Hackuarium/beemos/common/images/beeBackground.jpg

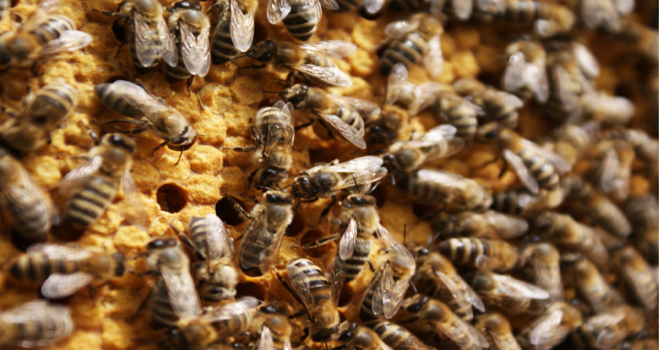
common/images/beeBackground.jpg
