Hackuarium/beemos/common/images/BeeMoSCounterPCB.jpg

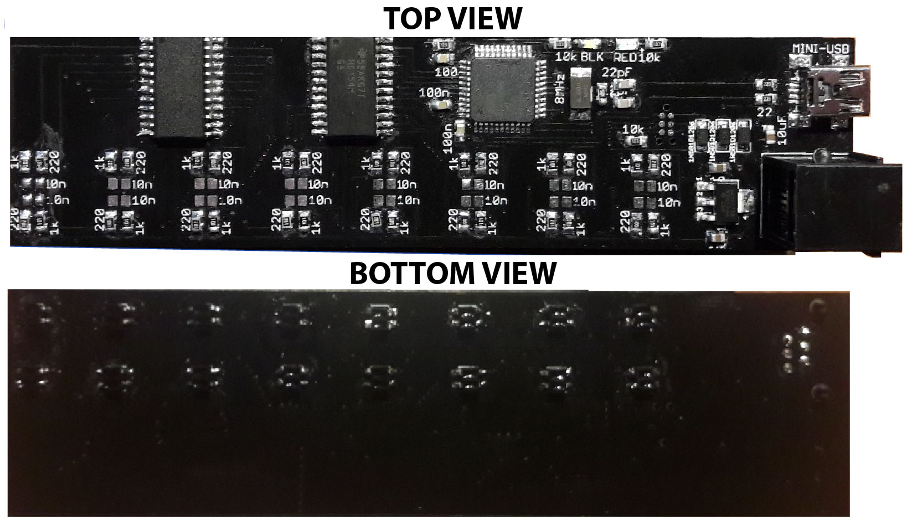
common/images/BeeMoSCounterPCB.jpg
