Hackuarium/beemos/scale-i2c/docs/balance2LoadCellsGlued.jpg

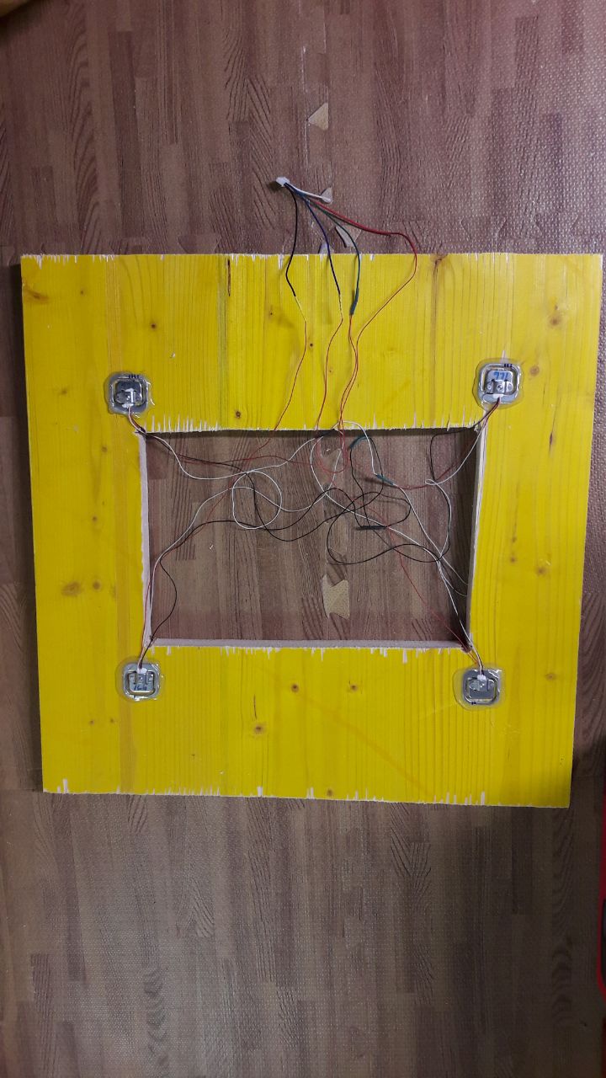
scale-i2c/docs/balance2LoadCellsGlued.jpg
