Hackuarium/beemos/scale-i2c/docs/closeUpBalance2Planed.jpg

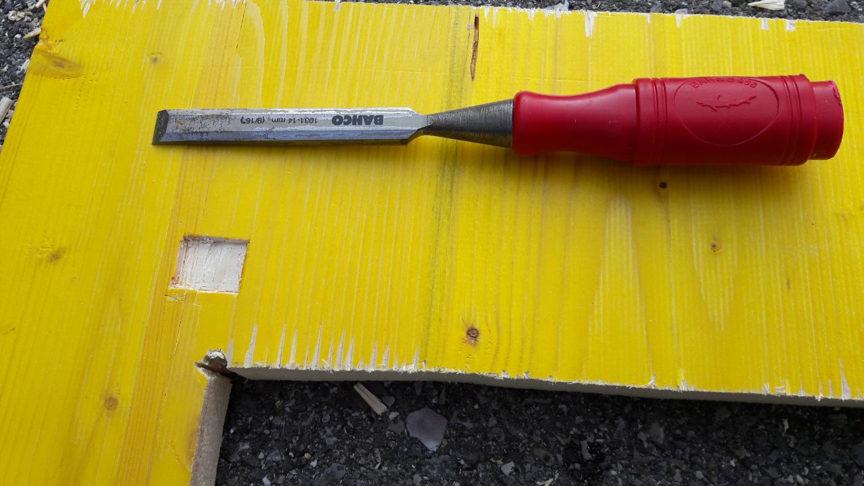
scale-i2c/docs/closeUpBalance2Planed.jpg
