Hackuarium/beemos/counter-i2c/arduino/Counter/Logger.ino

// part of the EEPROM is for the log
// we should be able to save and reload the log

#ifdef LOGGER


#define DATA_SIZE 920
#define DATA_TYPE 0  // LONG

// log is saved in the format ID / in1 / out1 / ... / in8 / out8
// ID is a sequential number
// We expect to add an entry every hour

#define NUMBER_PARAMETERS_TO_LOG  20
#define LOG_ENTRY_LENGTH          NUMBER_PARAMETERS_TO_LOG*2
#define NUMBER_LOGS               DATA_SIZE/LOG_ENTRY_LENGTH

#define FIRST_ADDRESS   1024-LOG_ENTRY_LENGTH*NUMBER_LOGS
#define LAST_ADDRESS   1023

unsigned long lastLog = millis();

void loggerInit() {
  // we need to reload the last ID
  setParameter(PARAM_LOGID, -1);
  for (byte i = 0; i < NUMBER_LOGS; i++) {
    int entryID =  eeprom_read_word((uint16_t*) (getFirstAddress(i)));
    if (entryID > getParameter(PARAM_LOGID)) {
      setParameter(PARAM_LOGID, entryID);
    }
  }
  for (byte i = 1; i < NUMBER_PARAMETERS_TO_LOG; i++) { // on boot counter is equal to 0
    setParameter(i, 0);
  }
  setParameter(PARAM_LOGID, getParameter(PARAM_LOGID) + 1);
  setParameter(PARAM_SECONDS, 0);
}


void writeLog() {
  int firstAddress = getFirstAddress(getParameter(PARAM_LOGID));
  for (byte i = 0; i < NUMBER_PARAMETERS_TO_LOG; i++) {
    eeprom_write_word((uint16_t*)  (firstAddress + i * 2), getParameter(i));
    if (i > 1) setParameter(i, 0);
  }
  setParameter(PARAM_LOGID, getParameter(PARAM_LOGID) + 1);
  lastLog = millis();
}

void readLog(byte entryID) {
  int firstAddress = getFirstAddress(entryID);
  for (byte i = 0; i < NUMBER_PARAMETERS_TO_LOG; i++) {
    setParameter(i, eeprom_read_word((uint16_t*) (firstAddress + i * 2)));
  }
}

int getFirstAddress(int entryID) {
  return FIRST_ADDRESS + LOG_ENTRY_LENGTH * (entryID % NUMBER_LOGS);
}

void formatLog() {
  for (int i = FIRST_ADDRESS; i <= LAST_ADDRESS; i++) {
    eeprom_write_byte(i, 0);
  }
  setParameter(PARAM_LOGID, 0);
}

void printLog(Print* output) {
  for (byte i = 0; i < NUMBER_LOGS; i++) {
    output->print(i);
    output->print(" ");
    int firstAddress = getFirstAddress(i);
    for (byte j = 0; j < NUMBER_PARAMETERS_TO_LOG; j++) {
      output->print((int)eeprom_read_word((uint16_t*) (firstAddress + j * 2)));
      output->print(" ");
    }
    output->println("");
  }
}

NIL_WORKING_AREA(waThreadLogger, 0);
NIL_THREAD(ThreadLogger, arg) {
  loggerInit();
  while (true) {
    nilThdSleepMilliseconds(1000);

    int counter = 0;
    while (counter < getParameter(PARAM_LOGGING_INTERVAL)) {
      nilThdSleepMilliseconds(1000);
      counter++;
    }

    if (getParameter(PARAM_LOGGING_INTERVAL) >= 300) {
      writeLog();
    }
  }
}

void printLoggerHelp(Print * output) {
  output->println(F("Logger help"));
  output->println(F("(ld) Dump"));
  output->println(F("(lf) Format"));
  // output->println(F("(ll) Current log"));
  // output->println(F("(lm) Multiple log"));
  output->println(F("(lw) Write log"));

}

void processLoggerCommand(char command, char* data, Print* output) {
  switch (command) {
    case 'd':
      printLog(output);
      break;
    case 'f':
      if (data[0] == '\0' || atoi(data) != 1234) {
        output->println(F("Format enter lf1234"));
      } else {
        output->println(F("Formatting"));
        formatLog();
        output->println("Done");
      }
      break;
    case 'l':
      break;
    case 'm':
      break;
    case 'w':
      writeLog();
      output->println(F("Log written and data cleared"));
      break;
    default:
      printLoggerHelp(output);
  }
}


#endif
