Hackuarium/beemos/master/arduino/master/SI7021.ino

#include "libino/Si7021/Si7021.cpp"

Weather sensor;

NIL_WORKING_AREA(waThreadSi7021, 50);
NIL_THREAD(ThreadSi7021, arg) {
  nilThdSleepMilliseconds(1000);
  sensor.begin();

  while (true) {
    setParameter(PARAM_INT_HUMIDITY,sensor.getRH());
    setParameter(PARAM_INT_TEMPERATURE,sensor.getTemp());
    if (getParameter(PARAM_INT_HUMIDITY)!=ERROR_VALUE && getParameter(PARAM_INT_TEMPERATURE)!=ERROR_VALUE) {
        nilThdSleepMilliseconds(1000);
    }
    nilThdSleepMilliseconds(1000);
  }
}
