Hackuarium/beemos/counter-i2c/arduino/Counter/SerialSpecific.ino

// testing serial monitoring commands.

void processSpecificCommand(char* data, char* paramValue, Print* output) {

  switch (data[0]) {
    case 'b':
      printBackground(output);
      break;
    case 'c':
      printCounter(output);
      break;
    case 'g':
      printGateInfo(output);
      break;
#ifdef LOGGER
    case 'l':
      processLoggerCommand(data[1], paramValue, output);
      break;
#endif
    case 'r':
      resetCounter();
      break;
    case 't':
      printTotal(output);
      break;
  }
}

void printSpecificHelp(Print * output) {
  output->println(F("(b)ackground"));
  output->println(F("(c)ounter"));
  output->println(F("(g)ate debug bg"));
#ifdef LOGGER
  output->println(F("(l)og"));
#endif
}
