Hackuarium/beemos/master/arduino/master/Sleep.ino

#include <avr/sleep.h>

void sleepNow () {
  // more information about sleep: https://www.nongnu.org/avr-libc/user-manual/group__avr__sleep.html

  nilSemWait(&lockTimeCriticalZone);         // make sure we don't get interrupted before we sleep
  wdt_disable();
  sleep_enable ();          // enables the sleep bit in the mcucr register
  sleepBefore();
  set_sleep_mode (SLEEP_MODE_PWR_DOWN);

  nilThdSleepMilliseconds(2);  // smll debouncing
  attachInterrupt (digitalPinToInterrupt (0), empty, CHANGE);

  nilSemSignal(&lockTimeCriticalZone);      // unprotectThread allowed now, next instruction WILL be executed
  sleep_cpu ();            // here the device is put to sleep

  sleep_disable ();         // first thing after waking from sleep:
  detachInterrupt (digitalPinToInterrupt (0));      // stop LOW interrupt on D2
  wdt_enable(WDTO_8S);  //reactivate the watchdog
  sleepAfter();
}

void empty() {}

void sleepBefore() {
  
}

void sleepAfter() {


}
